FrankBuss/beat707/vcvrack/Beat707/src_logic/Interface.cpp

/*
 * 
 * Created by William Kalfelz @ Beat707 (c) 2018 - http://www.Beat707.com
 * 
 */

#include "declarations.h"

// ------------------------------------------------------------------------------------------------------------------------------------------------------------------------------------------------------------------------------------------------
void createScreen()
{
  // Sequence Position ---------------------------------------------------------------------------------------------------------------- //
  leds[0] = leds[1] = leds[2] = 0;
  if (seqPlaying) leds[0] = leftLEDsVarSeq; else bitSet(leds[0], 0);
  //
  if (!seqPlaying)
  {
    byte xVar = variation;
    if (forceVariation >= 0) xVar = forceVariation;
    if (mirror) leds[0] |= 0B11110000; 
    else 
    {
      if (forceVariation >= 0)
      {
        leds[0] |= 0B11110000;
        bitClear(leds[0], xVar + 4);
      }
      else bitSet(leds[0], xVar + 4);
    }    
  }
  //
  // Pattern / Track Selection -------------------------------------------------------------------------------------------------------- //
  leds[1] = leds[2] = 0;
  //
  if (curRightScreen == kRightMenu && menuPosition >= menuEcho && menuPosition <= menuEchoType)
  {
    leds[1] = leds[2] = 0B01010101; 
  } 
  else if (curRightScreen == kRightMenu && (menuPosition == menuVariationsABCD || menuPosition == menuPtPlays || menuPosition == menuPtPlaysChain || menuPosition == menuPtNext))
  {
   leds[1] = leds[2] = 0B01010101; 
  }
  else if (curRightScreen == kRightMenu && menuPosition != menuMIDIChannel && menuPosition != menuNote && menuPosition != menuNoteLen && menuPosition != menuProc && menuPosition != menuVariationsABCD && !(menuPosition >= menuProgramChange && menuPosition <= menuMIDICCValueRate))
  {
    leds[1] = leds[2] = 0xFF;
  }
  else if (curRightScreen == kRightPatternSelection)
  {
    leds[1] = patternBitsSelector;
    leds[2] = patternBitsSelector >> 8;
  }
  else if (menuPosition == menuVariationsABCD)
  {
   leds[1] = leds[2] = 0B01010101; 
  }
  else
  {
    if (curRightScreen != kMuteMenu)
    {
      if (curTrack < 8) bitSet(leds[1], curTrack); else bitSet(leds[2], curTrack - 8);
    }
    //
    if (seqPlaying && curRightScreen != kRightTrackSelection)
    {
      leds[1] = leds[1] ^ chaseLEDs[0];
      leds[2] = leds[2] ^ chaseLEDs[1];
    }
  }
  //
  // Left Screen ---------------------------------------------------------------------------------------------------------------------- //
  if (curLeftScreen == kLeftMain)
  {
    if (editingNoteTranspose != -127 && !editingNote && curRightScreen == kRightSteps && curTrack >= DRUM_TRACKS)
    {
      if (noteTransposeEditAllSteps) 
      {
        segments[0][0] = S_A;
        printNumber(0, 1, editingNoteTranspose);
      }
      else 
      {
        segments[0][0] = S_N;
        byte holdingNote = 0;
        for (byte x=0; x<8; x++)
        {
          for (byte i=0; i<2; i++)
          {
            if (bitRead(buttonEventWasHolding[i + 1], x))
            {
              if (holdingNote == 0) holdingNote = stepsData[x + (i * 8)].noteSteps[curTrack-DRUM_TRACKS][editVariation];
              else
              {
                holdingNote = 0;
                break;
              }
            }
          }
        }
        //
        if (holdingNote == 0) printNumber(0, 1, editingNoteTranspose); 
        else 
        {
          segments[0][2] = 0;
          printNumber(0, 1, holdingNote);
        }
      }
    }
    else if (configData.midiClockInternal) 
    {
      segments[0][0] = S_b;
      printNumber(0, 1, configData.BPM);
    }
    else
    {
      segments[0][0] = S_b;
      segments[0][1] = S_E;
      segments[0][2] = S_X;
      segments[0][3] = S_T;
    }
    if (recordEnabled) segments[0][0] = S_R;
    //
    segments[0][4] = S_P;
    if (nextPattern != currentPattern) printNumber(0, 5, nextPattern + 1); else printNumber(0, 5, currentPattern + 1);
    if (streamNextPattern || loadPatternNow) segments[0][7] |= 0B10000000;
    //
    byte theBank = currentPatternBank + 1;
    if (currentPatternBank != nextPatternBank) theBank = nextPatternBank;
    segments[0][5] = getBankLetter(theBank);
    if (showBPMdot) segments[0][5] |= 0B10000000;
  }
  //
  resetSegments(1, 2);
  //
  if (temporaryMessageCounter > 0)
  {
    if (showTemporaryMessage == kMemoryProtectMessage) showMemoryProtected();
    else if (showTemporaryMessage == kPatternRepeatMessage)
    {
      if (repeatMode == kRepeatModeNormal)
      {
        segments[1][0] = S_N;
        segments[1][1] = S_O;
        segments[1][2] = S_R;
        segments[1][3] = S_N;
        segments[1][4] = S_N;
        segments[1][5] = S_A;
        segments[1][6] = S_L;
        //
        segments[2][0] = S_N;
        segments[2][1] = S_N;
        segments[2][2] = S_O;
        segments[2][3] = S_d;
        segments[2][4] = S_E;
      }
      else if (repeatMode == kRepeatModeChain)
      {
        segments[1][0] = S_R;
        segments[1][1] = S_E;
        segments[1][2] = S_P;
        segments[1][3] = S_E;    
        segments[1][4] = S_A;    
        segments[1][5] = S_T;    
        //
        segments[1][7] = S_C;
        segments[2][0] = S_U;
        segments[2][1] = S_R;
        //
        segments[2][3] = S_C;
        segments[2][4] = S_H;
        segments[2][5] = S_A;
        segments[2][6] = S_I;
        segments[2][7] = S_N;
      }
      else
      {
        segments[1][0] = S_R;
        segments[1][1] = S_E;
        segments[1][2] = S_P;
        segments[1][3] = S_E;    
        segments[1][4] = S_A;    
        segments[1][5] = S_T;    
        //
        segments[2][0] = S_1_;
        //
        segments[2][2] = S_P;
        segments[2][3] = S_A;
        segments[2][4] = S_T;
        segments[2][6] = S_R;
        segments[2][7] = S_N;        
      }
    }
    //
    temporaryMessageCounter++;
    if (temporaryMessageCounter >= TEMPORARY_MESSAGE_TIME)  temporaryMessageCounter = 0;
    return;
  }
  //
  //
  // MUTE Screen --------------------------------------------------------------------------------------------------------------------- //
  if (curRightScreen == kMuteMenu)
  {
    createScreenMute();
    return;
  }
  //
  //
  // Right Screen --------------------------------------------------------------------------------------------------------------------- //
  if (curRightScreen == kRightMenuCopyPaste)
  {
    showMenuCopyPaste();
  }
  else if (curRightScreen == kRightMenu)
  {
    showMenu();
  }
  else if (curRightScreen == kRightPatternSelection && forceAccent && isSelectingBank)
  {
    segments[1][0] = S_b;
    segments[1][1] = S_A;
    segments[1][2] = S_N;
    segments[1][3] = S_K;
    //
    segments[1][5] = S_S;
    segments[1][6] = S_E;
    segments[1][7] = S_L;
    segments[2][0] = S_E;
    segments[2][1] = S_C;
    segments[2][2] = S_T; 
    //
    segments[2][4] = S_1_;
    segments[2][5] = S_DASH;
    segments[2][6] = S_G;
  }
  else if (curRightScreen == kRightSteps || 
      curRightScreen == kRightTrackSelection ||
      curRightScreen == kRightABCDVariations ||
      curRightScreen == kRightPatternSelection)
  {
    //
    #if TRACK_DEBUG_MIDI
      if (curRightScreen == kRightTrackSelection)
      {
        printNumber2(1, 3, lastMIDIinput[3]);
        printNumber2(1, 7, lastMIDIinput[2]);
        printNumber2(2, 3, lastMIDIinput[1]);
        printNumber2(2, 7, lastMIDIinput[0]);
        return;
      }
    #endif
    //
    byte xVar = variation;
    if (forceVariation >= 0) xVar = forceVariation;
    //  
    if (curTrack < DRUM_TRACKS)
    {
      for (byte xs=0; xs < 2; xs++)
      {
        for (byte x=0; x < 8; x++)
        {       
          getStepVelocity(x + (xs*8), curTrack, xVar, false);
          //
          segments[xs + 1][x] = (char)stepChars[stepVelocity];
          //
          if (bitRead(stepsData[x + (xs*8)].stepsDouble[xVar], curTrack)) segments[xs + 1][x] |= 0B10000000;
        }
      }
    }
    else // NOTE TRACKS ---===----==---==-- //
    {
      if (editingNote)
      {
        getStepVelocity(editStep, curTrack, editVariation, false);
        xm = bitRead(stepsData[editStep].noteStepsExtras[curTrack-DRUM_TRACKS][1], 1 + (editVariation * 2)) << 1;
        xm |= bitRead(stepsData[editStep].noteStepsExtras[curTrack-DRUM_TRACKS][1], 0 + (editVariation * 2));
        //
        if (xm == 3) showOnOrOff(false);
        else if (stepsData[editStep].noteSteps[curTrack-DRUM_TRACKS][editVariation] > 0 && stepVelocity != 0)
        {
          printMIDInote(stepsData[editStep].noteSteps[curTrack-DRUM_TRACKS][editVariation], 2, 0, 3);
          segments[2][6] = S_U;
          segments[2][7] = (char)numbers[stepVelocity];
          //
          if (xm == 1) 
          {
            segments[1][0] = S_G;
            segments[1][1] = S_L;
            segments[1][2] = S_d;
            segments[1][3] = S_E;
          }
          else if (xm == 2) 
          {
            segments[1][0] = S_d;
            segments[1][1] = S_b;
            segments[1][2] = S_L;
            segments[1][3] = S_E;
          }
        }
        else
        {
          for (byte xs=0; xs < 8; xs++) { segments[2][xs + 8] = 0B01000000; }
        }
      }
      else // ----------------------------------------------------------------------------------- //
      {
        for (byte xs=0; xs < 2; xs++)
        {
          for (byte x=0; x < 8; x++)
          {
            xm = bitRead(stepsData[x + (xs*8)].noteStepsExtras[curTrack-DRUM_TRACKS][1], 1 + (xVar * 2)) << 1;
            xm |= bitRead(stepsData[x + (xs*8)].noteStepsExtras[curTrack-DRUM_TRACKS][1], 0 + (xVar * 2));
            getStepVelocity(x + (xs*8), curTrack, xVar, false);
            //
            if (xm != 3 && stepsData[x + (xs*8)].noteSteps[curTrack-DRUM_TRACKS][xVar] > 0 && stepVelocity != 0)
              segments[xs + 1][x] = (char)stepChars[stepVelocity];
            //
            if (xm == 1) segments[xs + 1][x] |= 0B01000000;
            else if (xm == 2) segments[xs + 1][x] |= 0B10000000;
            else if (xm == 3) segments[xs + 1][x] |= 0B01000000;            
          }
        }       
      }
    }
  }
}

/*
 * 0 Play
 * 1 Stop
 * 2 (-) >
 * 3 (+) > change tempo or any Menu option
 * 4 Switch Accent
 * 5 ABCD -> Mirror Mode
 * 6 Pattern Selection  >
 * 7 Track Selection    > Both = Menu
 */

// ------------------------------------------------------------------------------------------------------------------------------------------------------------------------------------------------------------------------------------------------
// ------------------------------------------------------------------------------------------------------------------------------------------------------------------------------------------------------------------------------------------------
// ------------------------------------------------------------------------------------------------------------------------------------------------------------------------------------------------------------------------------------------------
void checkInterface()
{
  if (curRightScreen == kMuteMenu) // MUTE Editing // ---------------------------------------------------------------------------------------------------------------------------------------------------------------------------------------------------------------- //
  {
    checkInterfaceMute();
    return;
  }
  //
  if (!somethingHappened) return;
  somethingHappened = false;
  //
  //
  // Start Sequencer //
  if (buttonEvent[0][0] >= kButtonClicked)
  {
    if (seqPlaying)
    {
      if (forceAccent)
      {
        repeatMode++;
        if (repeatMode > kRepeatModePattern) repeatMode = kRepeatModeNormal;
        ShowTemporaryMessage(kPatternRepeatMessage);       
      }
      else recordEnabled = !recordEnabled;
    }
    else
    {
      if (!seqPlaying && configData.midiClockInternal) startSequencer(false);
    }
    //
    buttonEvent[0][0] = 0;
  }
  //
  // Stop Sequencer //
  if (buttonEvent[0][1] >= kButtonClicked)
  {
    if (buttonEvent[0][1] == kButtonHold)
    {
        if (configData.midiClockInternal) 
        {
          recordEnabled = false;
          stopSequencer();
        }
    }
    buttonEvent[0][1] = 0;
    editingNoteTranspose = -127;
  }
  //
  // (-) BPM or Menu  // ---------------------------------------------------------------------------------------------------------------------------------------------------------------------------------------------------------------- //
  if (buttonEvent[0][2] >= kButtonClicked)
  {
    if (buttonEvent[0][2] == kButtonClicked)
    {
      if (editingNoteTranspose != -127 && curRightScreen == kRightSteps && curTrack >= DRUM_TRACKS)
      {
        bool foundOne = false;
        for (byte x=0; x<8; x++)
        {
          for (byte i=0; i<2; i++)
          {
            if ((noteTransposeEditAllSteps || bitRead(buttonEventWasHolding[i + 1], x)))
            {
              for (byte xp = 0; xp < 4; xp++)
              {
                if (!mirror) xp = editVariation;
                if (stepsData[x + (i * 8)].noteSteps[curTrack-DRUM_TRACKS][xp] > 0)
                {
                  stepsData[x + (i * 8)].noteSteps[curTrack-DRUM_TRACKS][xp]--;
                  patternData.lastNote[curTrack-DRUM_TRACKS] = stepsData[x + (i * 8)].noteSteps[curTrack-DRUM_TRACKS][xp];
                  //
                  if (!foundOne && editingNoteTranspose > -125) editingNoteTranspose--;
                  foundOne = true;                  
                }
                //
                if (!mirror) break;
              }
              //
              noteTransposeWasChanged = true;
            }
          }
        }
      }
      else if (curRightScreen == kRightMenu)
      {
        processMenu(-1);
      }
      else
      {
        if (configData.BPM > 40) 
        { 
          configData.BPM--;
          somethingChangedConfig = true;
        }
        updateSequencerSpeed(false);
      }
      updateScreen = true;
    }
    buttonEvent[0][2] = 0;
  }
  // (+) BPM or Menu  // ---------------------------------------------------------------------------------------------------------------------------------------------------------------------------------------------------------------- //
  if (buttonEvent[0][3] >= kButtonClicked)
  {
    if (forceAccent)
    {
      curRightScreen = kRightMenuCopyPaste;
      updateScreen = true;
    }
    else if (buttonEvent[0][3] == kButtonClicked)
    {
      if (editingNoteTranspose != -127 && curRightScreen == kRightSteps && curTrack >= DRUM_TRACKS)
      {
        bool foundOne = false;
        for (byte x=0; x<8; x++)
        {
          for (byte i=0; i<2; i++)
          {
            if ((noteTransposeEditAllSteps || bitRead(buttonEventWasHolding[i + 1], x)))
            {
              for (byte xp = 0; xp < 4; xp++)
              {
                if (!mirror) xp = editVariation;
                if (stepsData[x + (i * 8)].noteSteps[curTrack-DRUM_TRACKS][xp] < 127)
                {
                  stepsData[x + (i * 8)].noteSteps[curTrack-DRUM_TRACKS][xp]++;
                  patternData.lastNote[curTrack-DRUM_TRACKS] = stepsData[x + (i * 8)].noteSteps[curTrack-DRUM_TRACKS][xp];
                  //
                  if (!foundOne && editingNoteTranspose < 127) editingNoteTranspose++;
                  foundOne = true;                  
                }
                //
                if (!mirror) break;
              }
              //
              noteTransposeWasChanged = true;
            }
          }
        }
      }
      else if (curRightScreen == kRightMenu)
      {
        processMenu(1);
      }
      else
      {
        if (configData.BPM < 255)
        {
          configData.BPM++;
          somethingChangedConfig = true;
        }
        updateSequencerSpeed(false);
      }
      updateScreen = true;
    }
    buttonEvent[0][3] = 0;
  }
  //
  if (curRightScreen == kRightSteps) // Regular Steps Editing // ---------------------------------------------------------------------------------------------------------------------------------------------------------------------------------------------------------------- //
  {
    byte xVar = variation;
    if (forceVariation >= 0) xVar = forceVariation;
    if (mirror) xVar = 0;
    //  
    if (curTrack < DRUM_TRACKS)
    {
      for (byte x=0; x<8; x++)
      {
        for (byte i=0; i<2; i++)
        {
          if (buttonEvent[i + 1][x] > kButtonNone)
          {
            getStepVelocity(x + (i*8), curTrack, xVar, (buttonEvent[i + 1][x] == kButtonClicked));
            //
            if (buttonEvent[i + 1][x] == kButtonClicked)
            {
              somethingChangedPattern = true;
              //
              if (forceAccent)
              {
                if (stepVelocity == 0) stepVelocity = 1; 
                else if (stepVelocity == 1) stepVelocity = 2;
                else if (stepVelocity == 2) stepVelocity = 3;
                else if (stepVelocity == 3) stepVelocity = 1;
              }
              else
              {
                if (stepVelocity == 0) stepVelocity = 3; else stepVelocity = 0;
              }
              stepsData[x + (i*8)].steps[curTrack] |= stepVelocity << (xVar * 2);
              //
              if (mirror)
              {
                stepsData[x + (i*8)].steps[curTrack] = 0x00;
                stepsData[x + (i*8)].steps[curTrack] |= stepVelocity;
                stepsData[x + (i*8)].steps[curTrack] |= stepVelocity << 2;
                stepsData[x + (i*8)].steps[curTrack] |= stepVelocity << 4;
                stepsData[x + (i*8)].steps[curTrack] |= stepVelocity << 6;
              }
            }
            else if (buttonEvent[i + 1][x] == kButtonHold)
            {
              somethingChangedPattern = true;
              //
              if (bitRead(stepsData[x + (i*8)].stepsDouble[xVar], curTrack))
              {
                bitClear(stepsData[x + (i*8)].stepsDouble[xVar], curTrack);
                if (mirror)
                {
                  bitClear(stepsData[x + (i*8)].stepsDouble[1], curTrack);
                  bitClear(stepsData[x + (i*8)].stepsDouble[2], curTrack);
                  bitClear(stepsData[x + (i*8)].stepsDouble[3], curTrack);
                }
              }
              else
              {
                bitSet(stepsData[x + (i*8)].stepsDouble[xVar], curTrack);
                if (mirror)
                {
                  bitSet(stepsData[x + (i*8)].stepsDouble[1], curTrack);
                  bitSet(stepsData[x + (i*8)].stepsDouble[2], curTrack);
                  bitSet(stepsData[x + (i*8)].stepsDouble[3], curTrack);
                }
              }
            }
            //
            buttonEvent[i + 1][x] = 0;
            updateScreen = true;
          }
        }
      }
    }
    else // NOTE TRACKS // ---------------------------------------------------------------------------------------------------------------------------------------------------------------------------------------------------------------- //
    {
      for (byte x=0; x<8; x++)
      {
        for (byte i=0; i<2; i++)
        {
          if (buttonEvent[i + 1][x] > kButtonNone)
          {
            if (editingNote)
            {
              if (i == 1 && x == 7)  // Ok, close //
              {
                if (buttonEvent[i + 1][x] == kButtonClicked) editingNote = false;
              }
              else if (i == 1 && x == 6) // Octave
              {
                if (buttonEvent[i + 1][x] == kButtonClicked)
                {
                  uint16_t xNote = uint16_t(stepsData[editStep].noteSteps[curTrack-DRUM_TRACKS][editVariation]) + 12;
                  if (xNote > 108) xNote = uint16_t(stepsData[editStep].noteSteps[curTrack-DRUM_TRACKS][editVariation]) - ((uint16_t(stepsData[editStep].noteSteps[curTrack-DRUM_TRACKS][editVariation]) / 12) * 12);
                  if (xNote <= 0) xNote = 12;
                  stepsData[editStep].noteSteps[curTrack-DRUM_TRACKS][editVariation] = byte(xNote & 0B01111111);
                  patternData.lastNote[curTrack-DRUM_TRACKS] = stepsData[editStep].noteSteps[curTrack-DRUM_TRACKS][editVariation];
                  checkIfMirrorAndCopy(editStep, curTrack-DRUM_TRACKS);
                }
              }
              else if (i == 1 && x == 5) // Velocity
              {
                if (buttonEvent[i + 1][x] == kButtonClicked)
                {
                  getStepVelocity(editStep, curTrack, editVariation, true);
                  getNoteStepGlideDoubleOff(editStep, curTrack-DRUM_TRACKS, editVariation, true);
                  //
                  if (noteStepGlideDoubleOff == 3) 
                  {
                    noteStepGlideDoubleOff = 0;
                    stepVelocity = 1;
                  }
                  else if (stepVelocity == 1) stepVelocity = 2;
                  else if (stepVelocity == 2) stepVelocity = 3;
                  else noteStepGlideDoubleOff = 3;
                  lastVelocity = stepVelocity;
                  //
                  stepsData[editStep].noteStepsExtras[curTrack-DRUM_TRACKS][0] |= stepVelocity << (editVariation * 2);
                  stepsData[editStep].noteStepsExtras[curTrack-DRUM_TRACKS][1] |= noteStepGlideDoubleOff << (editVariation * 2); 
                  checkIfMirrorAndCopy(editStep, curTrack-DRUM_TRACKS);
                }
              }
              else if (i == 1 && x == 4) // Type (Glide or NoteOff / Hold=Double)
              {
                if (buttonEvent[i + 1][x] == kButtonClicked)
                {
                  getNoteStepGlideDoubleOff(editStep, curTrack-DRUM_TRACKS, editVariation, true);
                  //
                  if (noteStepGlideDoubleOff == 0) noteStepGlideDoubleOff = 1;
                  else if (noteStepGlideDoubleOff == 1) noteStepGlideDoubleOff = 2;
                  else if (noteStepGlideDoubleOff == 2) noteStepGlideDoubleOff = 3;
                  else noteStepGlideDoubleOff = 0;
                  //
                  stepsData[editStep].noteStepsExtras[curTrack-DRUM_TRACKS][1] |= noteStepGlideDoubleOff << (editVariation * 2); 
                  checkIfMirrorAndCopy(editStep, curTrack-DRUM_TRACKS);
                }
              }
              else // The other first 12 buttons for notes //
              {
                if (buttonEvent[i + 1][x] == kButtonClicked)
                {
                  byte xOct = stepsData[editStep].noteSteps[curTrack-DRUM_TRACKS][editVariation] / 12;
                  stepsData[editStep].noteSteps[curTrack-DRUM_TRACKS][editVariation] = (xOct * 12) + (x + (i * 8));
                  patternData.lastNote[curTrack-DRUM_TRACKS] = stepsData[editStep].noteSteps[curTrack-DRUM_TRACKS][editVariation];
                  checkIfMirrorAndCopy(editStep, curTrack-DRUM_TRACKS);
                }
              }
            }
            else // Not Editing Note // ---------------------------------------------------------------------------------------------------------------------------------------------------------------------------------------------------------------- //
            {
              somethingChangedPattern = true;
              //
              editStep = x + (i * 8);
              editVariation = xVar;
              getStepVelocity(editStep, curTrack, editVariation, false);
              //
              if (buttonEvent[i + 1][x] == kButtonClicked)
              {
                if (stepsData[editStep].noteSteps[curTrack-DRUM_TRACKS][editVariation] == 0 && patternData.lastNote[curTrack-DRUM_TRACKS] == 0)
                {
                  clearStepsExtrasBits(editStep, editVariation, curTrack-DRUM_TRACKS);
                  editingNote = true;
                  patternData.lastNote[curTrack-DRUM_TRACKS] = 60;
                  stepsData[editStep].noteSteps[curTrack-DRUM_TRACKS][editVariation] = patternData.lastNote[curTrack-DRUM_TRACKS];
                  stepsData[editStep].noteStepsExtras[curTrack-DRUM_TRACKS][0] |= lastVelocity << (editVariation * 2); 
                }
                else if (stepsData[editStep].noteSteps[curTrack-DRUM_TRACKS][editVariation] == 0 && patternData.lastNote[curTrack-DRUM_TRACKS] > 0)
                {
                  clearStepsExtrasBits(editStep, editVariation, curTrack-DRUM_TRACKS);
                  stepsData[editStep].noteSteps[curTrack-DRUM_TRACKS][editVariation] = patternData.lastNote[curTrack-DRUM_TRACKS];
                  stepsData[editStep].noteStepsExtras[curTrack-DRUM_TRACKS][0] |= lastVelocity << (editVariation * 2);
                }
                else if (forceAccent)
                {
                  getStepVelocity(editStep, curTrack, editVariation, true);
                  getNoteStepGlideDoubleOff(editStep, curTrack-DRUM_TRACKS, editVariation, true);
                  //
                  if (noteStepGlideDoubleOff == 3) 
                  {
                    noteStepGlideDoubleOff = 0;
                    stepVelocity = 1;
                  }
                  else if (stepVelocity == 1) stepVelocity = 2;
                  else if (stepVelocity == 2) stepVelocity = 3;
                  else noteStepGlideDoubleOff = 3;
                  lastVelocity = stepVelocity;
                  //
                  stepsData[editStep].noteStepsExtras[curTrack-DRUM_TRACKS][0] |= stepVelocity << (editVariation * 2);
                  stepsData[editStep].noteStepsExtras[curTrack-DRUM_TRACKS][1] |= noteStepGlideDoubleOff << (editVariation * 2); 
                  checkIfMirrorAndCopy(editStep, curTrack-DRUM_TRACKS);
                }               
                else if (stepsData[editStep].noteSteps[curTrack-DRUM_TRACKS][editVariation] > 0)
                {
                  getNoteStepGlideDoubleOff(editStep, curTrack-DRUM_TRACKS, editVariation, false);
                  //
                  if (noteStepGlideDoubleOff == 3)
                  {
                    bitClear(stepsData[editStep].noteStepsExtras[curTrack-DRUM_TRACKS][1], 1 + (editVariation * 2));
                    bitClear(stepsData[editStep].noteStepsExtras[curTrack-DRUM_TRACKS][1], 0 + (editVariation * 2));                                     
                    bitClear(stepsData[editStep].noteStepsExtras[curTrack-DRUM_TRACKS][0], 1 + (editVariation * 2));
                    bitClear(stepsData[editStep].noteStepsExtras[curTrack-DRUM_TRACKS][0], 0 + (editVariation * 2));                 
                  }
                  else if (stepVelocity == 0)
                  {
                    bitSet(stepsData[editStep].noteStepsExtras[curTrack-DRUM_TRACKS][0], 1 + (editVariation * 2));
                    bitSet(stepsData[editStep].noteStepsExtras[curTrack-DRUM_TRACKS][0], 0 + (editVariation * 2));
                  }
                  else
                  {
                    bitClear(stepsData[editStep].noteStepsExtras[curTrack-DRUM_TRACKS][0], 1 + (editVariation * 2));
                    bitClear(stepsData[editStep].noteStepsExtras[curTrack-DRUM_TRACKS][0], 0 + (editVariation * 2));                 
                  }
                }
                //
                checkIfMirrorAndCopy(editStep, curTrack-DRUM_TRACKS);
              }
              else if (buttonEvent[i + 1][x] == kButtonRelease)
              {
                editingNoteTranspose = -127;
              }
              else if (buttonEvent[i + 1][x] == kButtonReleaseNothingClicked && !forceAccent)
              {
                if (false) //!noteTransposeWasChanged)
                {
                  if (stepsData[editStep].noteSteps[curTrack-DRUM_TRACKS][editVariation] > 0 && stepVelocity == 0)
                  {
                    clearStepsExtrasBits(editStep, editVariation, curTrack-DRUM_TRACKS);
                    //
                    if (patternData.lastNote[curTrack-DRUM_TRACKS] == 0) patternData.lastNote[curTrack-DRUM_TRACKS] = 60;
                    stepsData[editStep].noteSteps[curTrack-DRUM_TRACKS][editVariation] = patternData.lastNote[curTrack-DRUM_TRACKS];
                    stepsData[editStep].noteStepsExtras[curTrack-DRUM_TRACKS][0] |= lastVelocity << (editVariation * 2);
                    //
                    checkIfMirrorAndCopy(editStep, curTrack-DRUM_TRACKS);
                    editingNote = false;
                  }
                  else if (stepsData[editStep].noteSteps[curTrack-DRUM_TRACKS][editVariation] == 0)
                  {
                    clearStepsExtrasBits(editStep, editVariation, curTrack-DRUM_TRACKS);
                    //
                    if (patternData.lastNote[curTrack-DRUM_TRACKS] == 0) patternData.lastNote[curTrack-DRUM_TRACKS] = 60;
                    stepsData[editStep].noteSteps[curTrack-DRUM_TRACKS][editVariation] = patternData.lastNote[curTrack-DRUM_TRACKS];
                    stepsData[editStep].noteStepsExtras[curTrack-DRUM_TRACKS][0] |= lastVelocity << (editVariation * 2);
                    //
                    checkIfMirrorAndCopy(editStep, curTrack-DRUM_TRACKS);
                    editingNote = false;
                  }
                  else
                  {
                    getNoteStepGlideDoubleOff(editStep, curTrack-DRUM_TRACKS, editVariation, false);
                    if (noteStepGlideDoubleOff == 3) editingNote = false;
                  }
                }
                //
                editingNoteTranspose = -127;
              }
            }
            buttonEvent[i + 1][x] = 0;
            updateScreen = true;
          }
        }
      }      
    }
  }
  //
  // ---------------------------------------------------------------------------------------------------------------------------------------------------------------------------------------------------------------- //
  // ---------------------------------------------------------------------------------------------------------------------------------------------------------------------------------------------------------------- //
  // ---------------------------------------------------------------------------------------------------------------------------------------------------------------------------------------------------------------- //
  //
  if (curRightScreen == kRightTrackSelection ||
      curRightScreen == kRightABCDVariations ||
      curRightScreen == kRightPatternSelection ||
      curRightScreen == kRightMenuCopyPaste ||
      curRightScreen == kRightMenu)
  {
    char leButton = -1;
    for (byte x=0; x<8; x++)
    {
      for (byte i=0; i<2; i++)
      {
        if (buttonEvent[i + 1][x] == kButtonClicked)
        {
          buttonEvent[i + 1][x] = 0;
          updateScreen = true;
          leButton = x + (i * 8);
        }
      }
    }
    //
    if (leButton >= 0)
    {
      if (curRightScreen == kRightMenu && menuPosition == menuInit)
      {
        processMenuOK();
      }
      else if (curRightScreen == kRightTrackSelection ||  curRightScreen == kRightMenu)
      {
        editingNote = false;
        curTrack = leButton; 
      }
      else if (curRightScreen == kRightABCDVariations)
      {
        if (leButton <= 3) forceVariation = leButton; else forceVariation = -1;
        mirror = false;
      }
      else if (curRightScreen == kRightMenuCopyPaste)
      {
        processMenuCopyPaste(leButton);
      }
      else if (curRightScreen == kRightPatternSelection)
      {
        checkIfDataNeedsSaving();
        //
        if (isSelectingBank)
        {
          bitSet(patternBitsSelector, leButton);
          nextPatternBank = leButton;
          nextPattern = 0;
        }
        else
        {
          bitSet(patternBitsSelector, leButton);
          nextPattern = leButton;
        }
        if (currentPattern != nextPattern || nextPatternBank != currentPatternBank) loadPattern(nextPattern);
      }
    }
  }
  //  
  // ---===------===------===------===------===------===------===------===---
  //
  if (curRightScreen == kRightMenu) buttonEvent[0][5] = 0;
  else
  {
    if (buttonEvent[0][5] == kButtonClicked)
    {
      checkMenuClose();
      buttonEvent[0][5] = 0;
      updateScreen = true;
      //
      if (forceAccent)
      {
        curRightScreen = kMuteMenu;
        forceAccent = false;
        isSelectingBank = false;
      }
      else
      {
        if (forceVariation >= 0)
        {
          mirror = false;
          forceVariation = -1;    
        }
        else
        {
          mirror = !mirror;
          forceVariation = -1;
        }
      }
    }
    else if (buttonEvent[0][5] == kButtonHold)
    {
      checkMenuClose();
      buttonEvent[0][5] = 0;
      curRightScreen = kRightABCDVariations;
    }
    else if (buttonEvent[0][5] > kButtonHold)
    {
      updateScreen = true;
      buttonEvent[0][5] = 0;
      curRightScreen = kRightSteps;
    }
  }
  //
  // ----------============------------
  //
  if (buttonEvent[0][7] == kButtonClicked)
  {
    updateScreen = true;
    buttonEvent[0][7] = 0;
  }
  else if (buttonEvent[0][7] == kButtonHold)
  {
    updateScreen = true;
    buttonEvent[0][7] = 0;
    if (curRightScreen == kRightMenu)
    {
      menuPosition++;
      initMode = 0;
      if (menuPosition > lastMenu) menuPosition = menuFirst;
      if (menuPosition == menuMIDICCLFO && patternData.sendCC[curTrack] == 0) menuPosition = menuPulseOut;
      if (menuPosition == menuEchoTicks && patternData.echoConfig[echoEdit].track == 0) menuPosition = menuClockType;
    }
    else if (forceAccent)
    {
      curRightScreen = kRightMenu;
      initMode = menuPosition = 0;
    }
    else if (editingNoteTranspose != -127)
    {
      noteTransposeEditAllSteps = !noteTransposeEditAllSteps;
    }
    else curRightScreen = kRightTrackSelection;
  }
  else if (buttonEvent[0][7] > kButtonHold)
  {
    if (curRightScreen == kRightTrackSelection) curRightScreen = kRightSteps;
    updateScreen = true;
    buttonEvent[0][7] = 0;
  }
  //
  // ----------============------------
  //
  if (buttonEvent[0][4] == kButtonHold)
  {
    checkMenuClose();
    buttonEvent[0][4] = 0;
    forceAccent = true;
    isSelectingBank = false;
    updateScreen = true;  
  }
  else if (buttonEvent[0][4] > kButtonHold ||
           buttonEvent[0][4] == kButtonClicked)
  {
    forceAccent = false;
    isSelectingBank = false;
    buttonEvent[0][4] = 0;
    updateScreen = true;  
    if (curRightScreen != kRightMenu) curRightScreen = kRightSteps;
  }
  //
  // ----------============------------
  //
  if (buttonEvent[0][6] == kButtonHold)
  {
    if (curRightScreen == kRightSteps) curRightScreen = kRightPatternSelection;
    isSelectingBank = false;
    buttonEvent[0][6] = 0;
    updateScreen = true;
  }
  else if (buttonEvent[0][6] > kButtonHold ||
           buttonEvent[0][6] == kButtonClicked)
  {
    isSelectingBank = false;
    //
    if (forceAccent)
    {
      curRightScreen = kRightPatternSelection;
      isSelectingBank = true;
    }
    else if (curRightScreen == kRightMenu)
    {
      if (menuPosition > menuFirst) menuPosition--; else menuPosition = lastMenu;
      if (menuPosition == menuMIDICCValueRate && patternData.sendCC[curTrack] == 0) menuPosition = menuMIDICC;
      if (menuPosition == menuEchoType && patternData.echoConfig[echoEdit].track == 0) menuPosition = menuEchoTrack;
      initMode = 0;
    }    
    else
    {
      if (buttonEvent[0][6] == kButtonReleaseNothingClicked) changePattern(1);
      curRightScreen = kRightSteps;
    }
    //
    buttonEvent[0][6] = 0;
    updateScreen = true;
  }
}

// ------------------------------------------------------------------------------------------------------------------------------------------------------------------------------------------------------------------------------------------------
void checkIfMirrorAndCopy(byte thestep, byte track)
{
  if (mirror)
  {
    stepsData[thestep].noteSteps[track][1] = stepsData[thestep].noteSteps[track][0];
    stepsData[thestep].noteSteps[track][2] = stepsData[thestep].noteSteps[track][0];
    stepsData[thestep].noteSteps[track][3] = stepsData[thestep].noteSteps[track][0];
    //
    stepsData[thestep].noteStepsExtras[track][0] &= 0B00000011;
    stepsData[thestep].noteStepsExtras[track][0] |= stepsData[thestep].noteStepsExtras[track][0] << 2;
    stepsData[thestep].noteStepsExtras[track][0] |= stepsData[thestep].noteStepsExtras[track][0] << 4;
    stepsData[thestep].noteStepsExtras[track][0] |= stepsData[thestep].noteStepsExtras[track][0] << 6;
    //
    stepsData[thestep].noteStepsExtras[track][1] &= 0B00000011;
    stepsData[thestep].noteStepsExtras[track][1] |= stepsData[thestep].noteStepsExtras[track][1] << 2;
    stepsData[thestep].noteStepsExtras[track][1] |= stepsData[thestep].noteStepsExtras[track][1] << 4;
    stepsData[thestep].noteStepsExtras[track][1] |= stepsData[thestep].noteStepsExtras[track][1] << 6;
  }    
}

// ------------------------------------------------------------------------------------------------------------------------------------------------------------------------------------------------------------------------------------------------
void clearStepsExtrasBits(byte thestep, byte xVar, byte track)
{
  bitClear(stepsData[thestep].noteStepsExtras[track][0], (editVariation * 2));
  bitClear(stepsData[thestep].noteStepsExtras[track][0], (editVariation * 2) + 1);
  bitClear(stepsData[thestep].noteStepsExtras[track][1], (editVariation * 2));
  bitClear(stepsData[thestep].noteStepsExtras[track][1], (editVariation * 2) + 1);
}

// ------------------------------------------------------------------------------------------------------------------------------------------------------------------------------------------------------------------------------------------------
void resetSegments(byte xs, byte xe)
{
  for (byte xx = xs; xx <= xe; xx++) { memset(segments[xx], 0, sizeof(segments[0])); }
}

// ------------------------------------------------------------------------------------------------------------------------------------------------------------------------------------------------------------------------------------------------
void printStopSequencer()
{
  leds[0] = leds[1] = leds[2] = 0;
  resetSegments(1, 2);
  segments[1][4] = S_S;
  segments[1][5] = S_T;
  segments[1][6] = S_O;
  segments[1][7] = S_P;
  //
  segments[2][0] = S_S;
  segments[2][1] = S_E;
  segments[2][2] = S_O;
  segments[2][3] = S_U;
  segments[2][4] = S_E;
  segments[2][5] = S_N;
  segments[2][6] = S_C;
  segments[2][7] = S_R;
  //
  sendScreen();
  waitMs(2000);
  updateScreen = true;
}

// ------------------------------------------------------------------------------------------------------------------------------------------------------------------------------------------------------------------------------------------------
void getStepVelocity(byte theStep, byte track, byte variation, bool cleanBits)
{
  if (track < DRUM_TRACKS)
  {
    stepVelocity = bitRead(stepsData[theStep].steps[track], 1 + (variation * 2)) << 1;
    stepVelocity |= bitRead(stepsData[theStep].steps[track], 0 + (variation * 2));  
  }
  else
  {
    stepVelocity = bitRead(stepsData[theStep].noteStepsExtras[track-DRUM_TRACKS][0], 1 + (variation * 2)) << 1;
    stepVelocity |= bitRead(stepsData[theStep].noteStepsExtras[track-DRUM_TRACKS][0], 0 + (variation * 2));
  }
  //
  if (cleanBits)
  {
    if (track < DRUM_TRACKS)
    {
      bitClear(stepsData[theStep].steps[track], 1 + (variation * 2));
      bitClear(stepsData[theStep].steps[track], 0 + (variation * 2));   
    }
    else
    {
      bitClear(stepsData[theStep].noteStepsExtras[track-DRUM_TRACKS][0], (variation * 2));
      bitClear(stepsData[theStep].noteStepsExtras[track-DRUM_TRACKS][0], (variation * 2) + 1);                  
    }
  }
}

// ------------------------------------------------------------------------------------------------------------------------------------------------------------------------------------------------------------------------------------------------
void getNoteStepGlideDoubleOff(byte theStep, byte track, byte variation, bool cleanBits)
{
  noteStepGlideDoubleOff  = bitRead(stepsData[theStep].noteStepsExtras[track][1], 1 + (variation * 2)) << 1;
  noteStepGlideDoubleOff |= bitRead(stepsData[theStep].noteStepsExtras[track][1], 0 + (variation * 2));
  //
  if (cleanBits)
  {
    bitClear(stepsData[theStep].noteStepsExtras[track][1], (variation * 2));
    bitClear(stepsData[theStep].noteStepsExtras[track][1], (variation * 2) + 1);                  
  }
}

// ------------------------------------------------------------------------------------------------------------------------------------------------------------------------------------------------------------------------------------------------
char stepBeenHold()
{
  char holdingNote = -2;
  for (byte x=0; x<8; x++)
  {
    for (byte i=0; i<2; i++)
    {
      if (bitRead(buttonEventWasHolding[i + 1], x))
      {
        if (holdingNote == -2) holdingNote = stepsData[x + (i * 8)].noteSteps[curTrack-DRUM_TRACKS][editVariation]; else return -1;
      }
    }
  }
  return holdingNote;
}

// ------------------------------------------------------------------------------------------------------------------------------------------------------------------------------------------------------------------------------------------------
void ShowTemporaryMessage(byte message)
{
  showTemporaryMessage = message;
  temporaryMessageCounter = 1;
}

// ------------------------------------------------------------------------------------------------------------------------------------------------------------------------------------------------------------------------------------------------
void showOnOrOff(bool showOn)
{
  if (showOn)
  {
    segments[2][6] = S_O;
    segments[2][7] = S_N;
  }
  else
  {
    segments[2][5] = S_O;
    segments[2][6] = S_F;
    segments[2][7] = S_F;
  }
}

// ------------------------------------------------------------------------------------------------------------------------------------------------------------------------------------------------------------------------------------------------
void showMemoryProtected()
{
  segments[1][0] = S_P;
  segments[1][1] = S_R;
  segments[1][2] = S_O;
  segments[1][3] = S_T;
  segments[1][4] = S_E;
  segments[1][5] = S_C;
  segments[1][6] = S_T;
  //
  showOnOrOff(configData.writeProtectFlash);
}

// ------------------------------------------------------------------------------------------------------------------------------------------------------------------------------------------------------------------------------------------------
char getBankLetter(byte value)
{
  if (value <= 9) return (char)numbers[value];
  else if (value == 10) return S_A;
  else if (value == 11) return S_b;
  else if (value == 12) return S_C;
  else if (value == 13) return S_d;
  else if (value == 14) return S_E;
  else if (value == 15) return S_F;
  else return S_G;
}
