FrankBuss/beat707/vcvrack/Beat707/src_logic/Extras.cpp

/*
 * 
 * Created by William Kalfelz @ Beat707 (c) 2018 - http://www.Beat707.com
 * 
 */

#include "declarations.h"

// ------------------------------------------------------------------------------------------------------------------------------------------------------------------------------------------------------------------------------------------------
void reset()
{
  createFlashHeader();
  resetSegments(0, 2);
  memset(midiOutputBufferDT, 0, sizeof(midiOutputBufferDT));
  memset(midiOutputBufferNT, 0, sizeof(midiOutputBufferNT));
  memset(echoSpace, 0, sizeof(echoSpace));
  memset(echoAttackDecay, 0, sizeof(echoAttackDecay));
  memset(echoTrack, 0, sizeof(echoTrack));
  memset(echoCounter, 0, sizeof(echoCounter));
  memset(echoVelocity, 0, sizeof(echoVelocity));  
  memset(echoNote, 0, sizeof(echoNote));
  memset(leds, 0, sizeof(leds));
  memset(buttons, 0, sizeof(buttons));  
  memset(buttonEvent, 0, sizeof(buttonEvent));
  memset(buttonDownTime, 0, sizeof(buttonDownTime));
  memset(prevPlayedNote, 0, sizeof(prevPlayedNote));
  configData.init();
  bitSet(patternBitsSelector,0);
  midiOutputBufferDTPosition = midiOutputBufferNTPosition = 0;
  memset(recordBuffer, 0, sizeof(recordBuffer));
  recordBufferPosition = 0;
  memset(sendCCCurrentValue, 0, sizeof(sendCCCurrentValue));
  memset(sendCCCurrentPosition, 0, sizeof(sendCCCurrentPosition));
  memset(noteLenCounters, 0, sizeof(noteLenCounters));
  //
  resetPatternBank();
}

// ------------------------------------------------------------------------------------------------------------------------------------------------------------------------------------------------------------------------------------------------
void resetPatternBank()
{
  for (byte x=0; x < STEPS; x++) { stepsData[x].init(); }
  patternData.init();  
  //
  #if DEBUG_MIDI_INPUT
    memset(midiInput, 0, sizeof(midiInput));
    midiInputItens = 0;
  #endif 
}
